eez-open/ltc-an104-transient-tester/ac-powered/Transient tester r2B1 (bottom).png

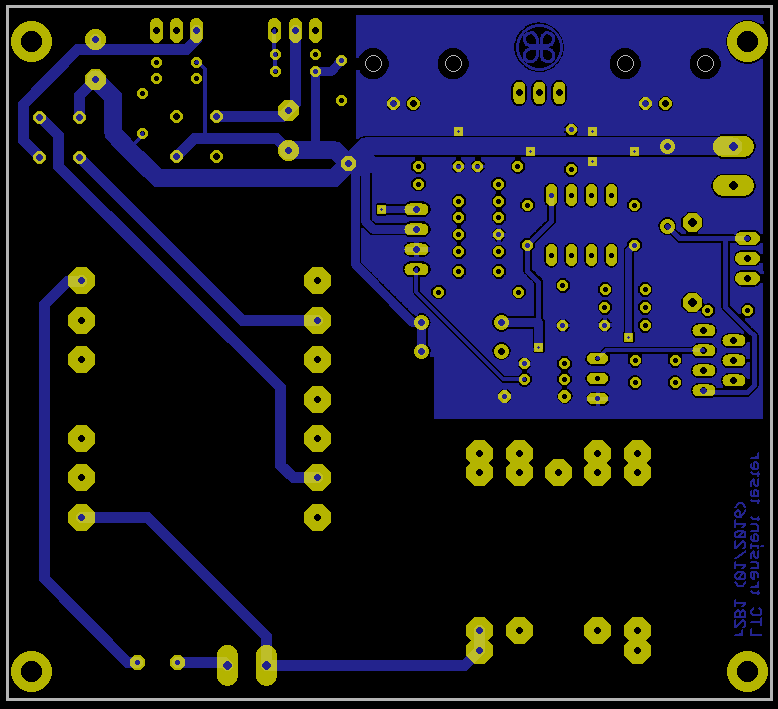
ac-powered/Transient tester r2B1 (bottom).png
